cskilbeck/volume_knob/images/hid_configurator_1.png

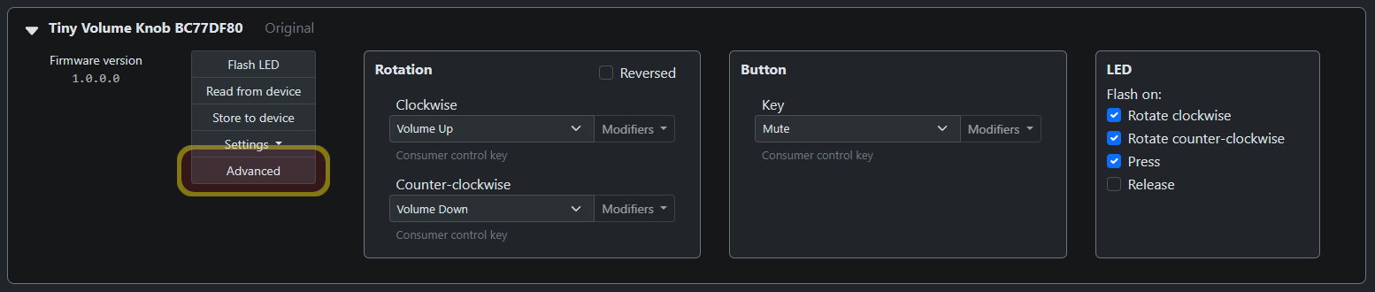
images/hid_configurator_1.png
