cskilbeck/volume_knob/pcb/wch554g/Outputs/2022-06-14/dfm.png

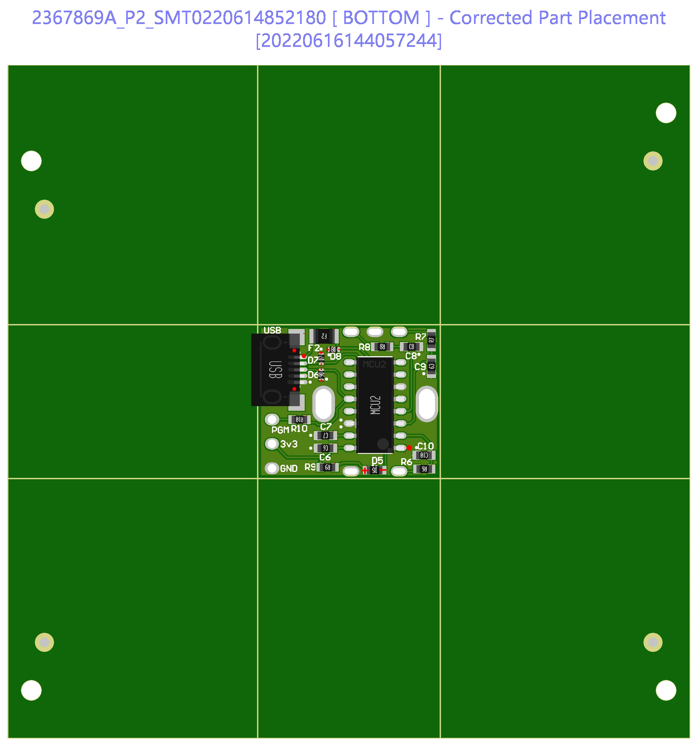
pcb/wch554g/Outputs/2022-06-14/dfm.png
