cskilbeck/volume_knob/enclosures/enclosure16x19/knob.SLDPRT

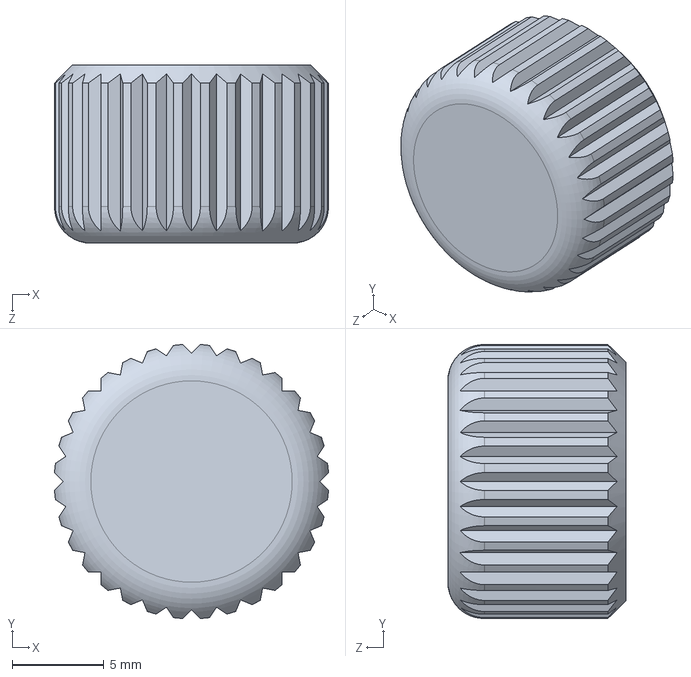
[picture p23: CAD file, 2022-03-15]
enclosures/enclosure16x19/knob.SLDPRT
15.0 x 15.0 x 9.75 mm
