cskilbeck/volume_knob/enclosures/enclosure_V2/enclosure_V2_lower.STEP

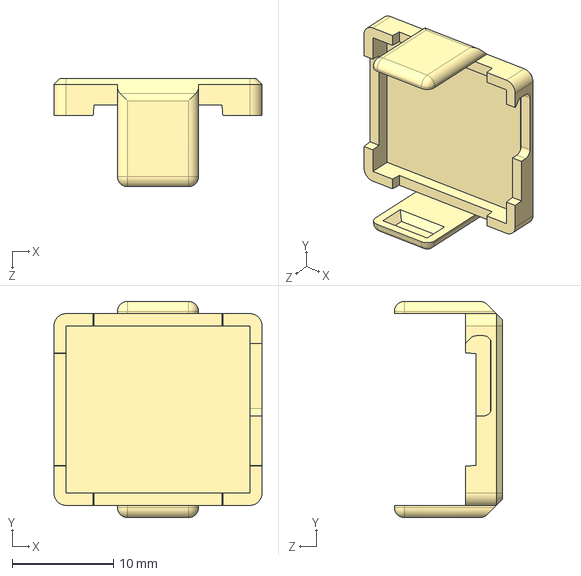
[picture p24: CAD file, 2025-02-15]
enclosures/enclosure_V2/enclosure_V2_lower.STEP
20.5 x 21.3 x 10.7 mm
