cskilbeck/volume_knob/enclosures/TUVK_Enclosure.step

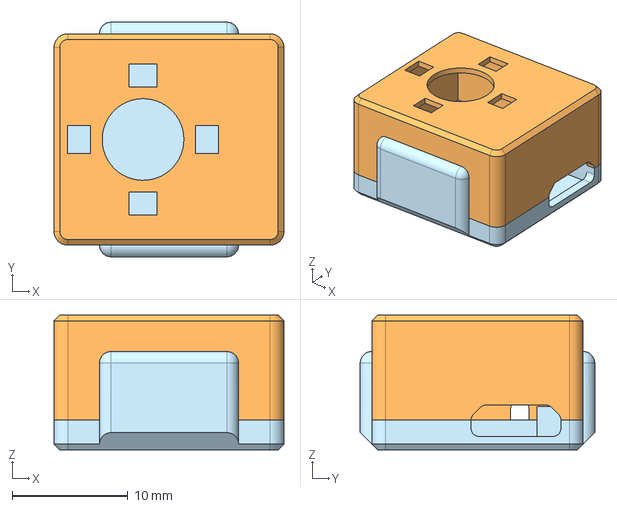
[picture p25: CAD file, 2026-02-22]
enclosures/TUVK_Enclosure.step
19.9 x 20.2 x 11.7 mm
