cskilbeck/volume_knob/pcb/wch554e/wch554e/Models/encoder.step

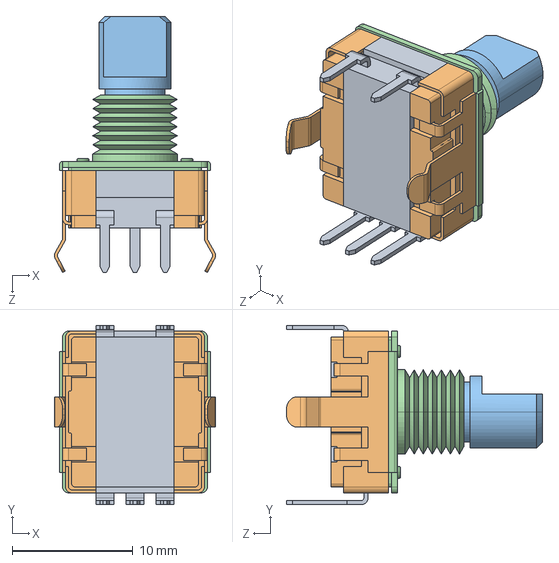
[picture p26: CAD file, 2022-03-15]
pcb/wch554e/wch554e/Models/encoder.step
13.4 x 14.9 x 21.2 mm
