cskilbeck/volume_knob/pcb/wch554g/models/U254-051T-4BH83-F1S--3DModel-STEP-510211.STEP

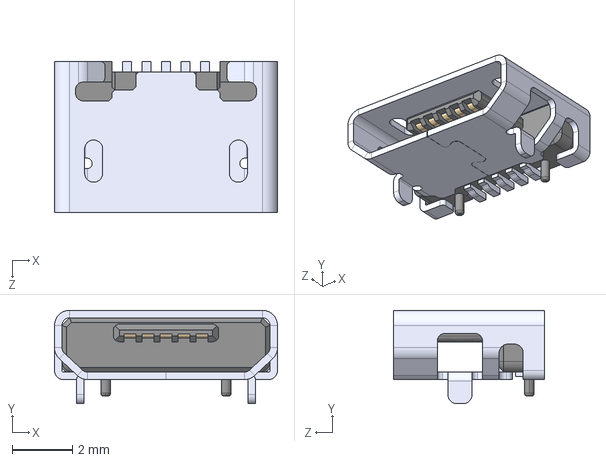
[picture p27: CAD file, 2023-11-22]
pcb/wch554g/models/U254-051T-4BH83-F1S--3DModel-STEP-510211.STEP
7.40 x 3.10 x 5.00 mm
