cskilbeck/volume_knob/enclosures/enclosure16x19/lower.SLDPRT

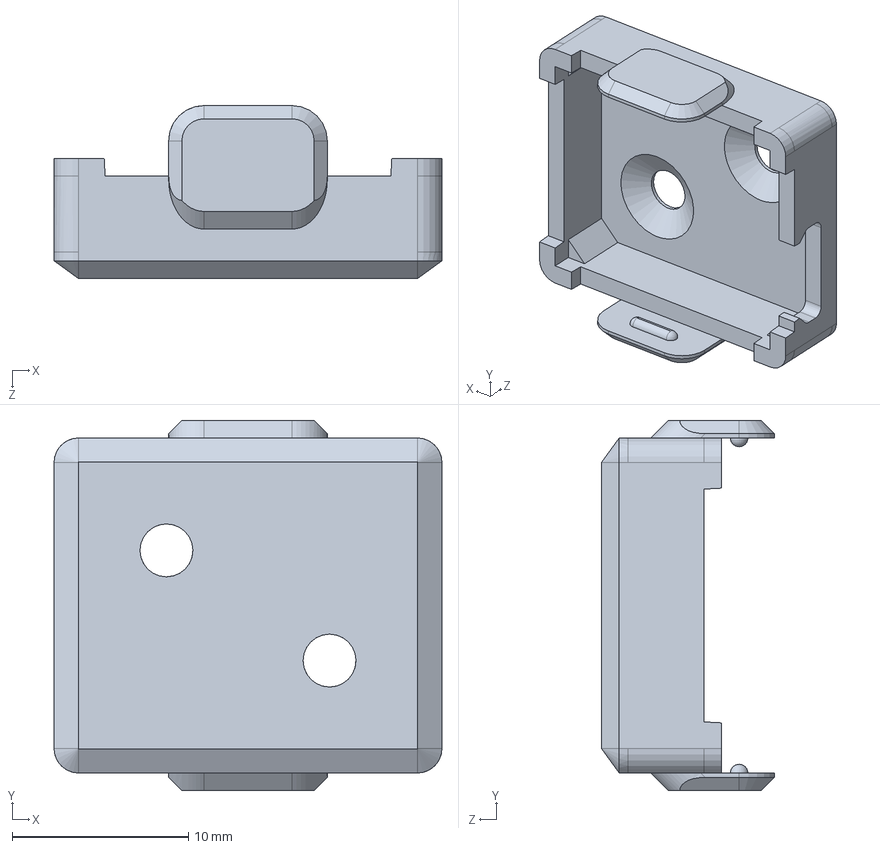
[picture p28: CAD file, 2022-03-15]
enclosures/enclosure16x19/lower.SLDPRT
22.0 x 21.0 x 9.80 mm
