cskilbeck/volume_knob/enclosures/enclosure_ch554e_80/knob.SLDPRT

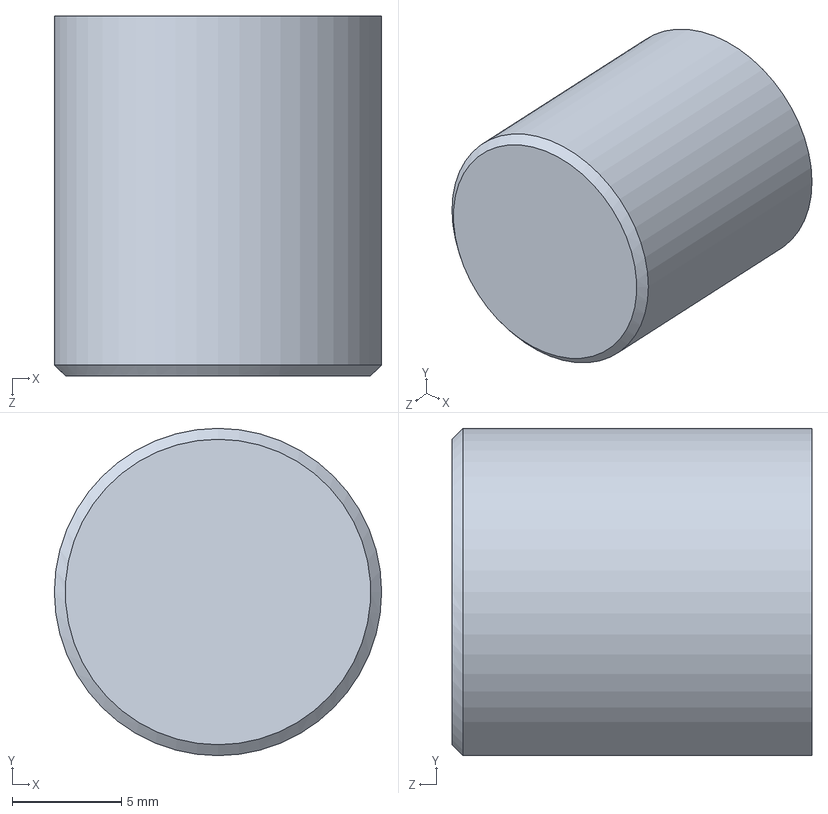
[picture p29: CAD file, 2024-07-27]
enclosures/enclosure_ch554e_80/knob.SLDPRT
15.0 x 15.0 x 16.5 mm
