cskilbeck/volume_knob/enclosures/enclosure_V2/enclosure_V2_upper.STEP

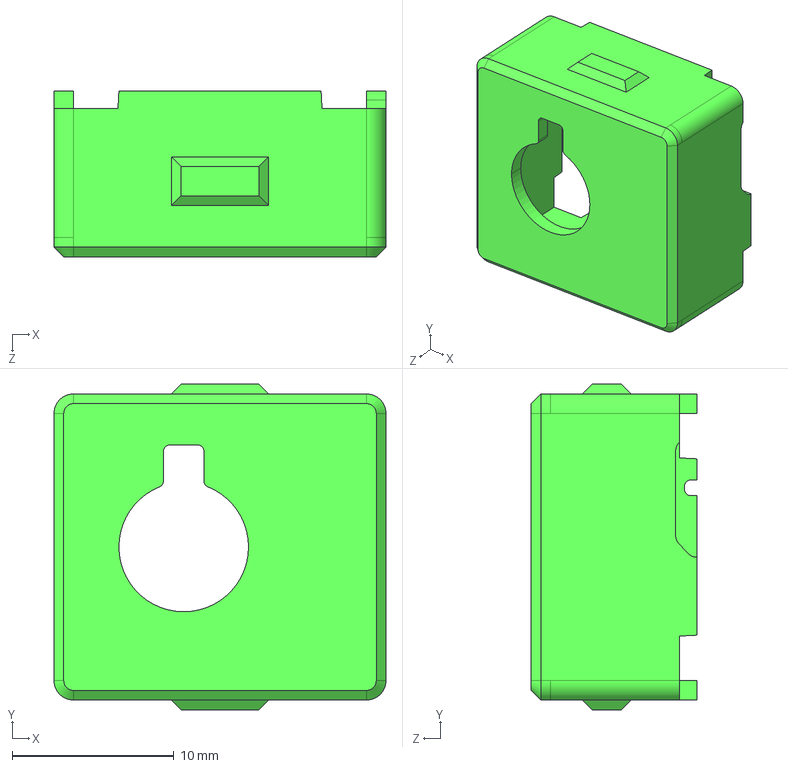
[picture p30: CAD file, 2025-02-15]
enclosures/enclosure_V2/enclosure_V2_upper.STEP
20.5 x 20.1 x 10.2 mm
