cskilbeck/volume_knob/enclosures/VK_D2.step

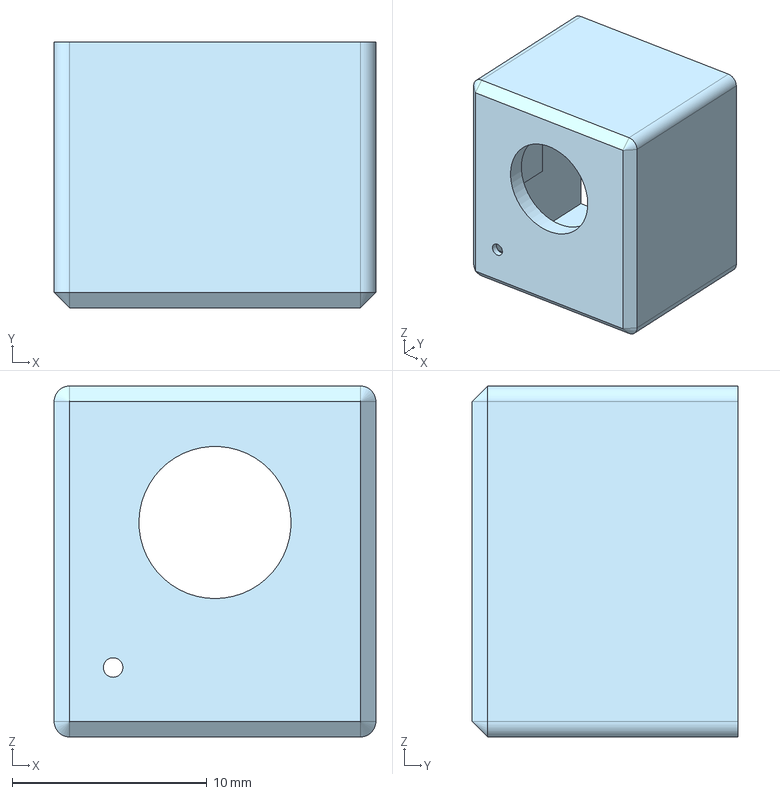
[picture p31: CAD file, 2026-02-22]
enclosures/VK_D2.step
16.5 x 13.7 x 18.0 mm
