cskilbeck/volume_knob/enclosures/enclosure_ch554e_80/lower.SLDPRT

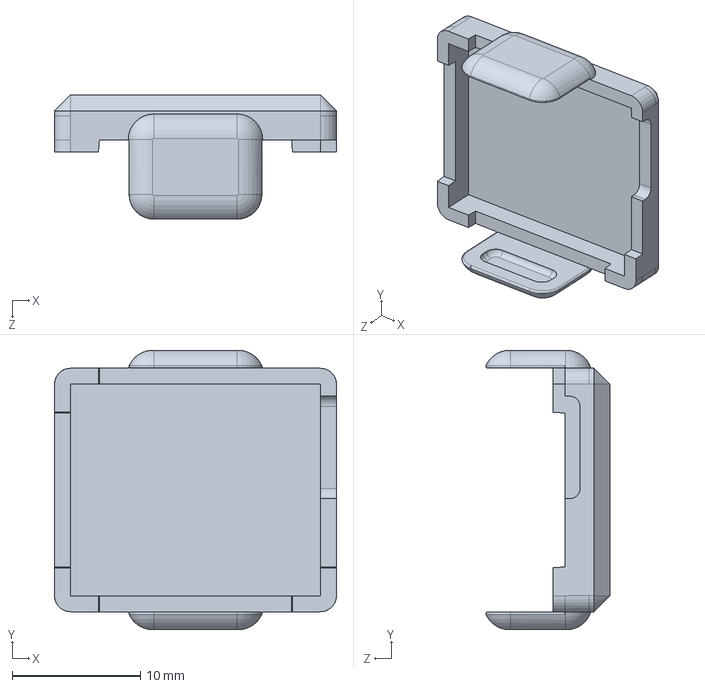
[picture p32: CAD file, 2024-06-04]
enclosures/enclosure_ch554e_80/lower.SLDPRT
22.0 x 21.8 x 9.71 mm
