cskilbeck/volume_knob/enclosures/enclosure16x19/encoder2.SLDPRT

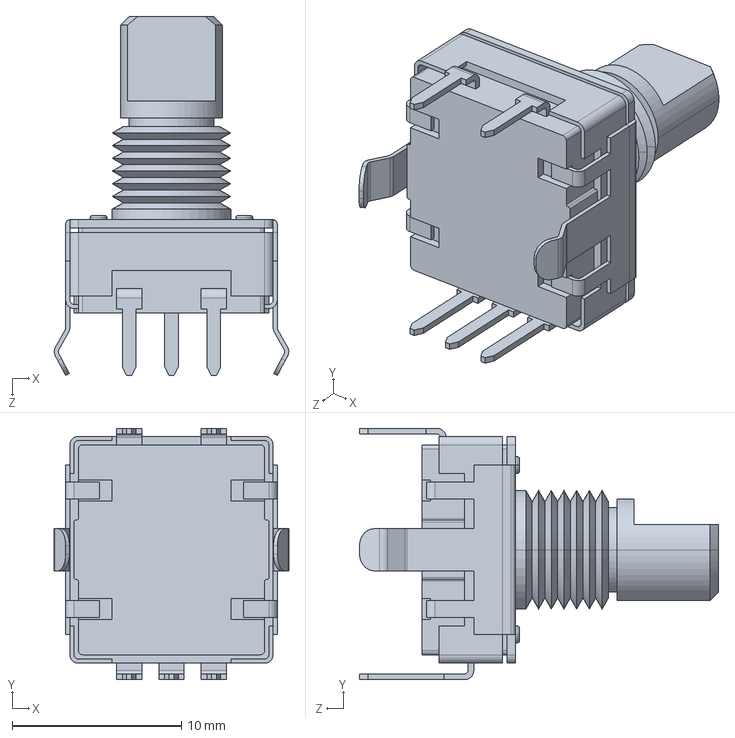
[picture p33: CAD file, 2022-03-15]
enclosures/enclosure16x19/encoder2.SLDPRT
13.9 x 14.9 x 21.2 mm
