cskilbeck/volume_knob/enclosures/enclosure_ch554e_80/upper.SLDPRT

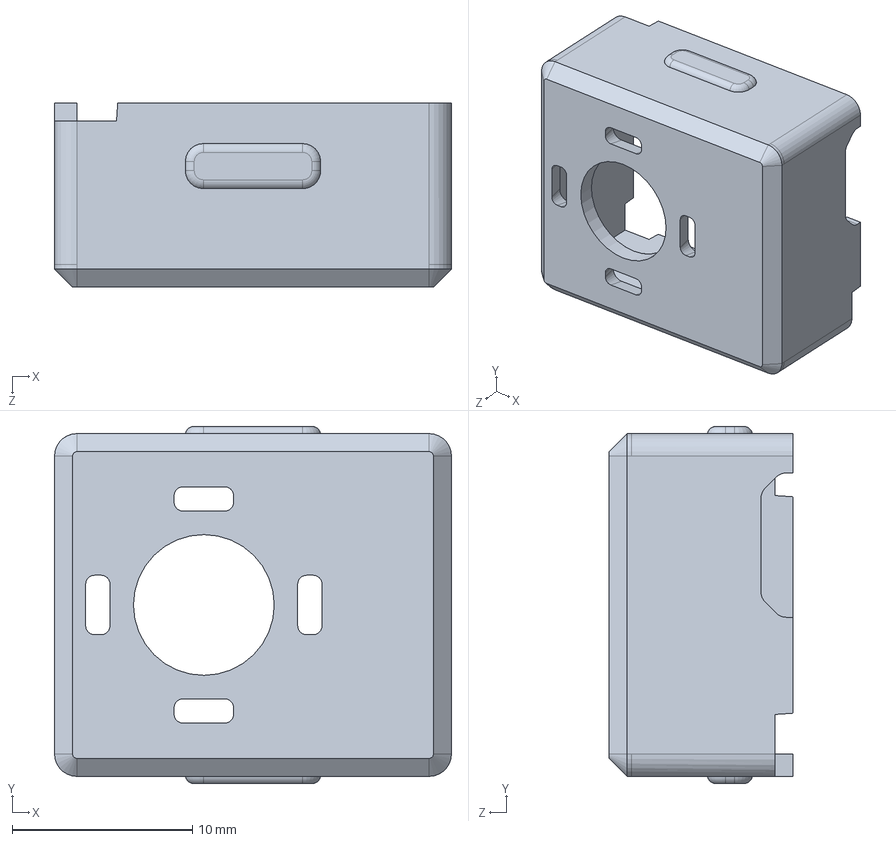
[picture p34: CAD file, 2024-06-04]
enclosures/enclosure_ch554e_80/upper.SLDPRT
22.0 x 19.8 x 10.2 mm
