cskilbeck/volume_knob/enclosures/enclosure_V2/PCB_V2.step

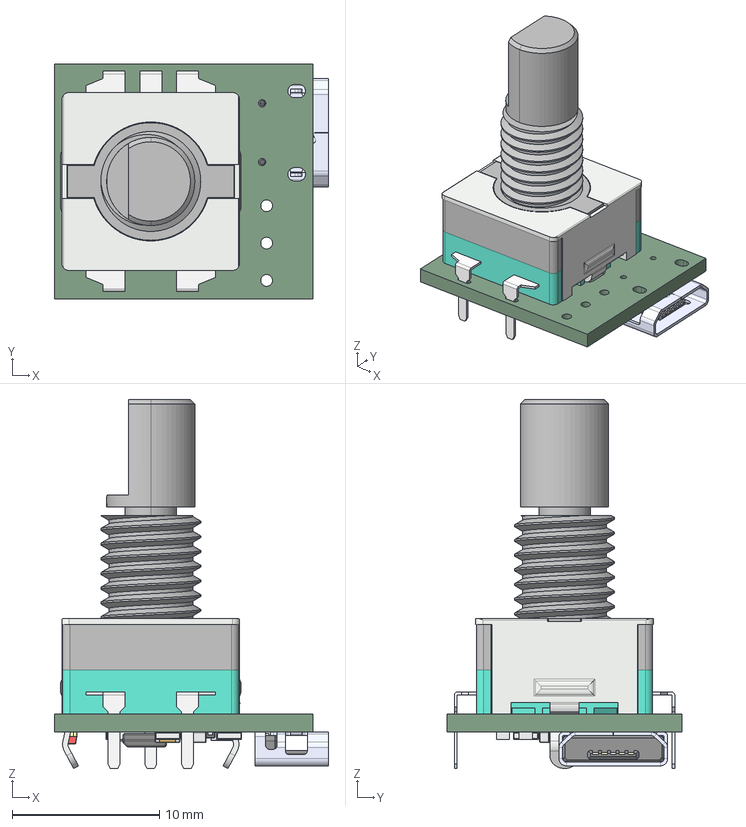
[picture p35: CAD file, 2024-10-21]
enclosures/enclosure_V2/PCB_V2.step
18.7 x 16.0 x 25.1 mm
Mid_Body x 5
Open_CASCADE_STEP_translator_6.8_12.2.1 x 11
Mark x 5
0603_Chip_SMD_LED_(1.6x0.8mm)_coloured
Open_CASCADE_STEP_translator_6.8_12.1
Leader x 10
rotary_encoder
U254-051T-4BH83-F1S_U254-051T-4BH83-F1S
FUSE_0603_1608_0.5MM
Open_CASCADE_STEP_translator_6.8_2.1.1 x 3
lead x 6
Open_CASCADE_STEP_translator_6.8_14.1.1 x 2
Open_CASCADE_STEP_translator_6.8_14.1.2 x 2
Open_CASCADE_STEP_translator_6.8_14.2.1 x 2
