cskilbeck/volume_knob/enclosures/enclosure_ch554e_80/usb_socket.STEP

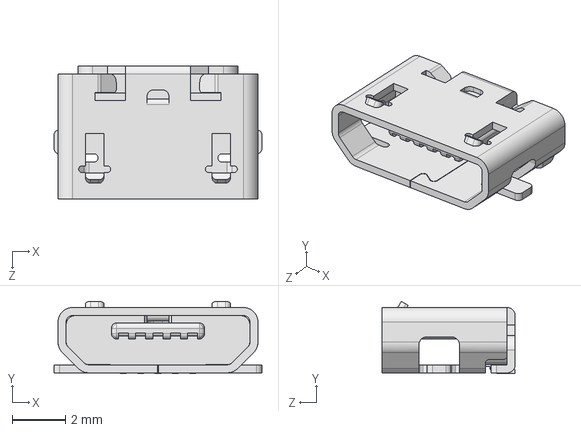
[picture p36: CAD file, 2024-03-06]
enclosures/enclosure_ch554e_80/usb_socket.STEP
7.80 x 2.71 x 5.00 mm
