cskilbeck/volume_knob/enclosures/enclosure_ch554e_80/board.SLDPRT

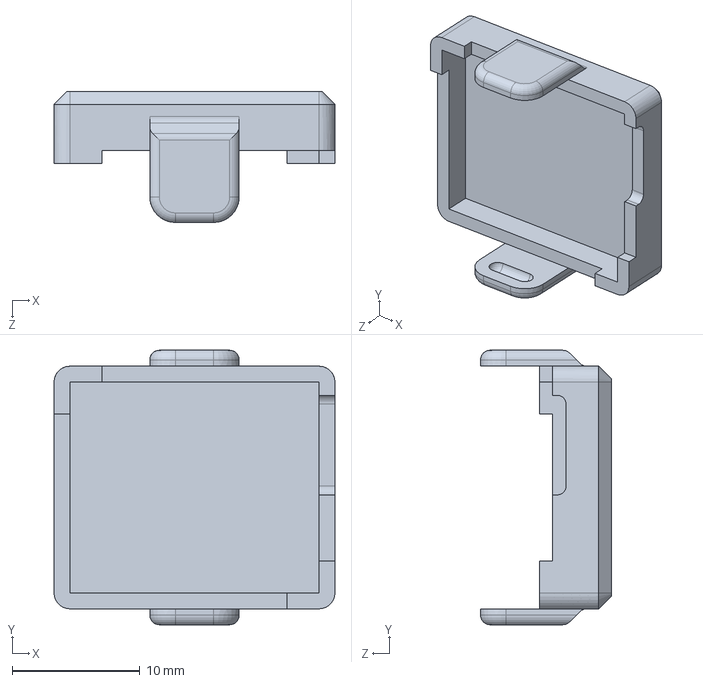
[picture p37: CAD file, 2022-04-18]
enclosures/enclosure_ch554e_80/board.SLDPRT
22.0 x 21.5 x 10.2 mm
