cskilbeck/volume_knob/pcb/wch554e/wch554e/Outputs/2022-03-28/wch554e.PDF

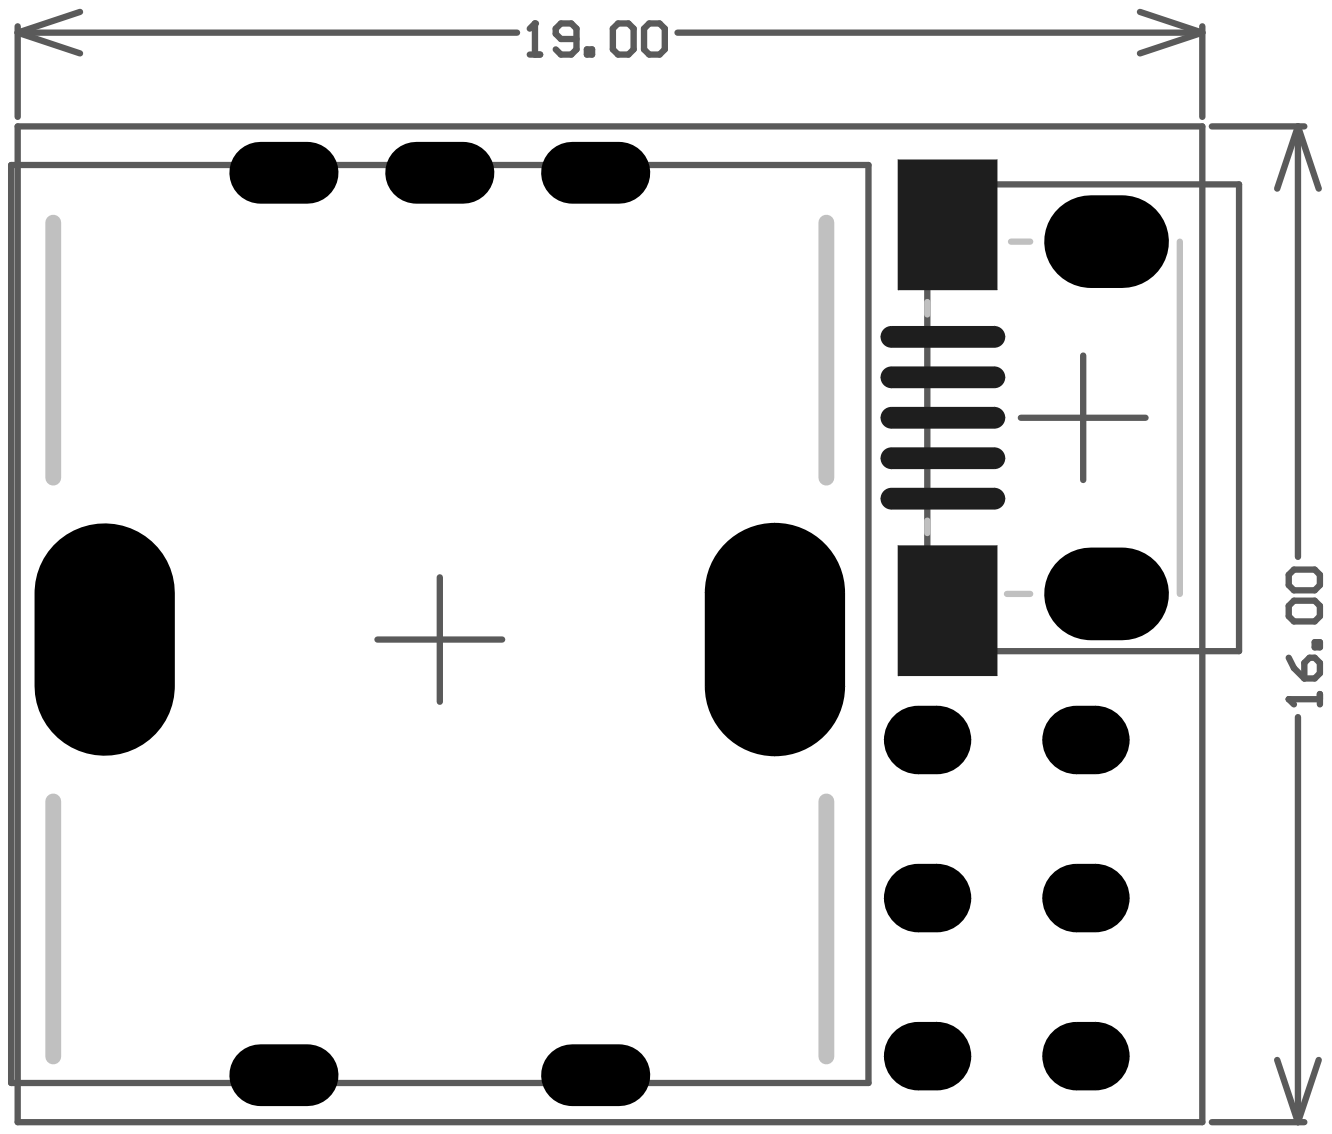
[picture p87: page 1]

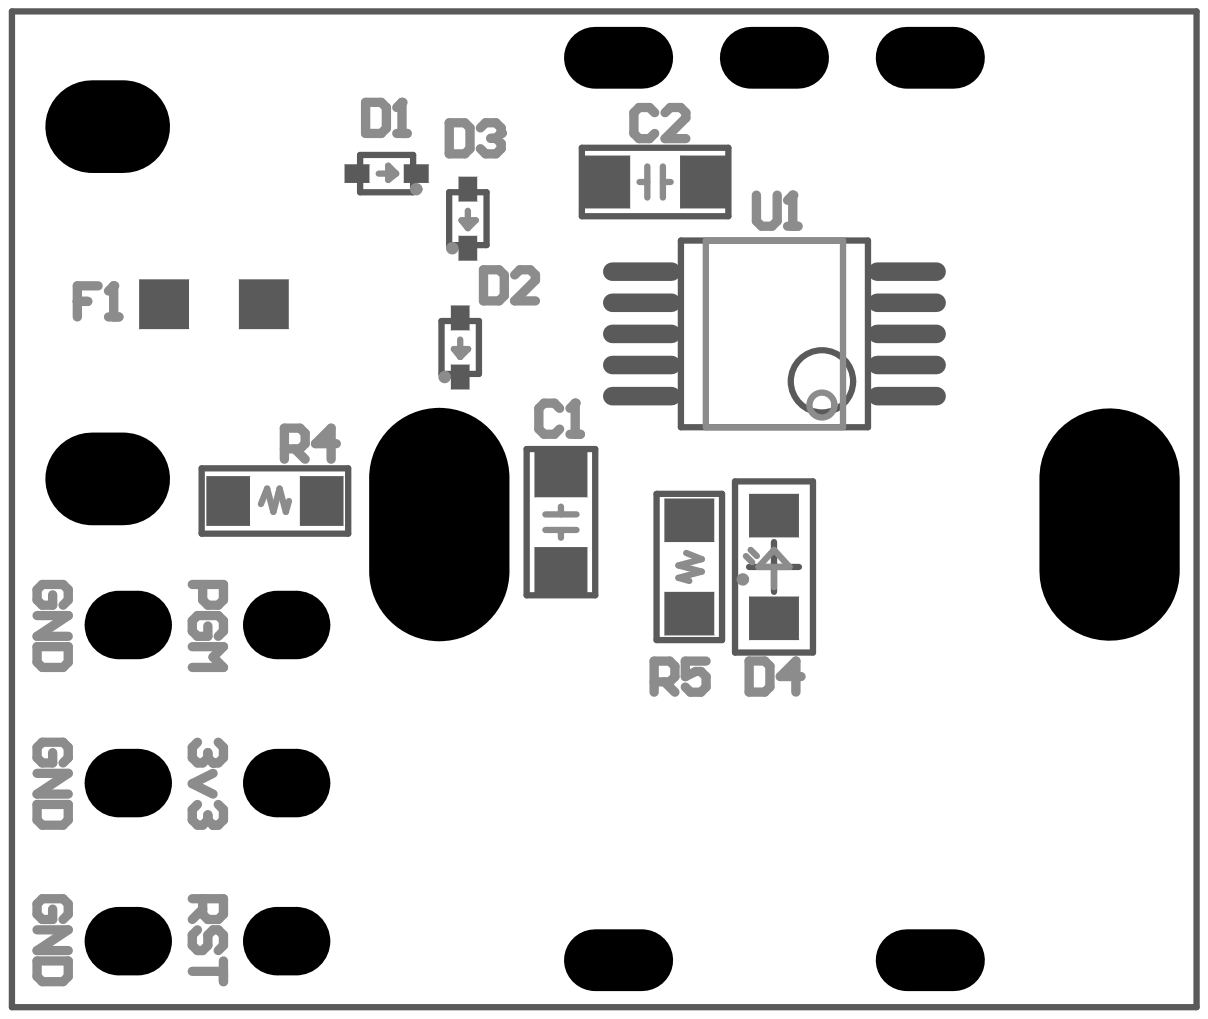
[picture p88: page 2]


P1.7/SCK/TXD1/TIN5 4

RST/T2EX_/CAP2_ 5 | DP | | D+ 3

Shield S

Designator | Quantity | Value | Description | Model:Footprint | Line #
U1 | 1 | | CH554E | MSOP10 3x3 x 0.5
DBG | 1 | | Debug header | 4 way debug header
F1 | 1 500mA | | FUSE | FUSE 0603
D4 | 1 20mA | | LED | SMT LED 0603
C1 | 1 1uF | | MLCC | MLCC 0603
C2 | 1 2.2uF | | MLCC | MLCC 0603
R4 | 1 10k | | Resistor | 0603 SMT Resistor
R5 | 1 1k | | Resistor | 0603 SMT Resistor
ROTARY_ENCODER | 1 | | Rotary Encoder | Rotary encoder
D1, D2, D3 | 3 | | TVS Diode | SODFL 98x40 2 pin
J1 | 1 | | USB Receptacle | USB Micro B Receptacle

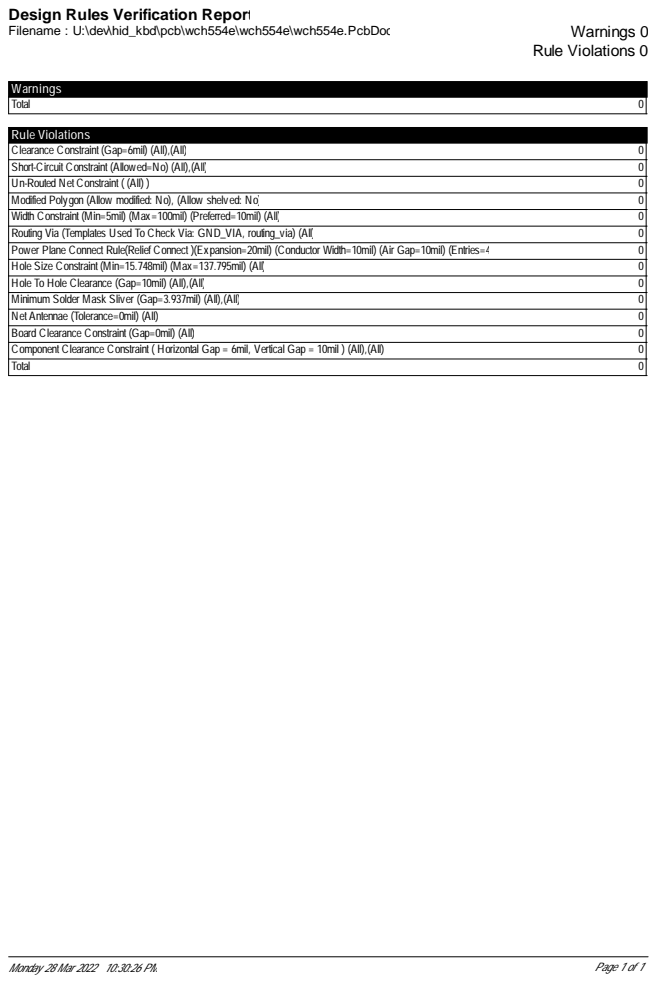
[picture p89: page 5]

Design Rules Verification Report
