cskilbeck/volume_knob/mic_muter/mic_muter/resource.h

//{{NO_DEPENDENCIES}}
// Microsoft Visual C++ generated include file.
// Used by mic_muter.rc
//
#define IDC_MYICON                      2
#define IDD_MICMUTER_DIALOG             102
#define IDS_APP_TITLE                   103
#define IDM_ABOUT                       104
#define IDI_MICMUTER                    107
#define IDC_MICMUTER                    109
#define ID_IMG_MUTED                    110
#define ID_IMG_NOT_MUTED                111
#define IDR_MAINFRAME                   128
#define IDI_ICON_MIC_GREEN              133
#define IDI_ICON_MIC_NORMAL             133
#define IDI_ICON_MIC_MUTE               134
#define IDR_MENU_POPUP                  135
#define IDI_ICON_MIC_MISSING            140
#define IDD_DIALOG_OPTIONS_OVERLAY      141
#define IDD_DIALOG_OPTIONS              142
#define IDC_SLIDER2                     1001
#define IDC_CHECK_RUN_AT_LOGIN          1003
#define IDC_CHECK_SHOW_WHEN_MUTED       1004
#define IDC_CHECK_SHOW_WHEN_UNMUTED     1005
#define IDC_SLIDER4                     1006
#define IDC_SLIDER5                     1007
#define IDC_SLIDER6                     1008
#define IDC_SLIDER7                     1009
#define IDC_STATIC_OVERLAY_POS          1012
#define IDC_CHECK_RUN_AT_STARTUP        1013
#define IDC_SLIDER1                     1022
#define IDC_COMBO_FADEOUT_AFTER         1023
#define IDC_COMBO_FADEOUT_TO            1024
#define IDC_COMBO_FADEOUT_SPEED         1025
#define IDC_CHECK_OVERLAY_ENABLE        1026
#define IDC_OPTIONS_TAB_CTRL            1037
#define IDC_STATIC_OPTIONS_OVERLAY_IMAGE 1038
#define IDC_BUTTON_CHOOSE_HOTKEY        1043
#define IDC_COMBO_HOTKEY                1046
#define IDC_CHECK_CTRL                  1047
#define IDC_CHECK_ALT                   1048
#define IDC_CHECK_SHIFT                 1049
#define IDC_CHECK4                      1050
#define IDC_CHECK_WINKEY                1050
#define IDC_STATIC_HOTKEY_MESSAGE       1051
#define ID_POPUP_QUIT                   32771
#define ID_POPUP_ETC                    32772
#define ID_POPUP_OPTIONS                32773
#define ID_POPUP_MUTE                   32774
#define ID_POPUP_MUTE2                  32775
#define ID_POPUP_OVERLAY                32776
#define ID_OVERLAY_POSITION             32777
#define ID_OVERLAY_MUTED                32778
#define ID_MUTED_ENABLE                 32779
#define ID_MUTED_FADEOUTAFTER           32780
#define ID_FADEOUTAFTER_1SECOND         32781
#define ID_FADEOUTAFTER_5SECONDS        32782
#define ID_FADEOUTAFTER_10SECONDS       32783
#define ID_FADEOUTAFTER_NEVER           32784
#define ID_MUTED_FADETO                 32785
#define ID_FADETO_INVISIBLE             32786
#define ID_OVERLAY_UNMUTED              32790
#define ID_UNMUTED_ENABLE               32791
#define ID_UNMUTED_FADEOUTAFTER         32792
#define ID_UNMUTED_FADETO               32797
#define ID_OPTIONS_RUNMICMUTERATLOGIN   32802
#define ID_POPUP_MICMUTER               32803
#define ID_POPUP_                       32804
#define ID_FADEOUTAFTER_1SECOND_MUTED   32805
#define ID_FADEOUTAFTER_5SECONDS_MUTED  32806
#define ID_FADEOUTAFTER_10SECONDS_MUTED 32807
#define ID_FADEOUTAFTER_NEVER_MUTED     32808
#define ID_FADETO_INVISIBLE_MUTED       32809
#define ID_FADETO_25_MUTED              32810
#define ID_FADETO_50_MUTED              32811
#define ID_FADEOUTAFTER_1SECOND_UNMUTED 32812
#define ID_FADEOUTAFTER_5SECONDS_UNMUTED 32813
#define ID_FADEOUTAFTER_10SECONDS_UNMUTED 32814
#define ID_FADEOUTAFTER_NEVER_UNMUTED   32815
#define ID_FADETO_INVISIBLE_UNMUTED     32816
#define ID_FADETO_25_UNMUTED            32817
#define ID_FADETO_50_UNMUTED            32818
#define ID_POPUP_ABOUTMICMUTER          32819
#define ID_MUTED_FADESPEED              32820
#define ID_FADESPEED_SLOW               32821
#define ID_FADESPEED_MEDIUM             32822
#define ID_FADESPEED_FAST               32823
#define ID_FADESPEED_IMMEDIATE          32824
#define ID_FADESPEED_SLOW_MUTED         32825
#define ID_FADESPEED_MEDIUM_MUTED       32826
#define ID_FADESPEED_FAST_MUTED         32827
#define ID_FADESPEED_IMMEDIATE_MUTED    32828
#define ID_FADESPEED_SLOW_UNMUTED       32829
#define ID_FADESPEED_MEDIUM_UNMUTED     32830
#define ID_FADESPEED_FAST_UNMUTED       32831
#define ID_FADESPEED_IMMEDIATE_UNMUTED  32832
#define ID_POPUP_SHOW_OPTIONS           32833
#define ID_POPUP_TOGGLE_MUTE            32834
#define ID_MOVE_OVERLAY                 32835
#define ID_POPUP_MOVE_OVERLAY           32836
#define IDC_STATIC                      -1

// Next default values for new objects
// 
#ifdef APSTUDIO_INVOKED
#ifndef APSTUDIO_READONLY_SYMBOLS
#define _APS_NO_MFC                     1
#define _APS_NEXT_RESOURCE_VALUE        143
#define _APS_NEXT_COMMAND_VALUE         32837
#define _APS_NEXT_CONTROL_VALUE         1052
#define _APS_NEXT_SYMED_VALUE           112
#endif
#endif
