cskilbeck/volume_knob/mic_muter/mic_muter/image.cpp

//////////////////////////////////////////////////////////////////////

#include "framework.h"

//////////////////////////////////////////////////////////////////////

namespace
{

#include "images/microphone_mute_svg.h"
#include "images/microphone_normal_svg.h"
#include "images/microphone_base_svg.h"

    char const *overlay_svg[chs::mic_muter::num_overlay_ids] = { microphone_mute_svg, microphone_normal_svg,
                                                                 microphone_base_svg };
}

namespace chs::mic_muter
{
    //////////////////////////////////////////////////////////////////////

    HRESULT image::create_solid(uint32 argb, int w, int h)
    {
        uint32 stride = w * sizeof(uint32);
        uint32 img_size = h * stride;

        BITMAPV5HEADER bmi{};
        bmi.bV5Size = sizeof(BITMAPV5HEADER);
        bmi.bV5Width = w;
        bmi.bV5Height = -h;
        bmi.bV5Planes = 1;
        bmi.bV5BitCount = 32;
        bmi.bV5Compression = BI_BITFIELDS;
        bmi.bV5SizeImage = img_size;
        bmi.bV5RedMask = 0x00ff0000;
        bmi.bV5GreenMask = 0x0000ff00;
        bmi.bV5BlueMask = 0x000000ff;
        bmi.bV5AlphaMask = 0xff000000;
        bmi.bV5CSType = LCS_WINDOWS_COLOR_SPACE;
        bmi.bV5Intent = LCS_GM_GRAPHICS;

        BITMAPINFO src_bmi{};
        src_bmi.bmiHeader.biSize = sizeof(BITMAPINFOHEADER);
        src_bmi.bmiHeader.biWidth = w;
        src_bmi.bmiHeader.biHeight = -h;
        src_bmi.bmiHeader.biPlanes = 1;
        src_bmi.bmiHeader.biBitCount = 32;
        src_bmi.bmiHeader.biCompression = BI_RGB;

        dc = CreateCompatibleDC(nullptr);

        uint32 *buffer = new uint32[img_size];

        for(uint32 i = 0; i < img_size; ++i) {
            buffer[i] = argb;
        }

        DEFER(delete[] buffer);

        bmp = CreateDIBitmap(dc, (BITMAPINFOHEADER const *)&bmi, CBM_INIT, buffer, &src_bmi, DIB_RGB_COLORS);
        if(bmp == nullptr) {
            return WIN32_LAST_ERROR("CreateDIBitmap");
        }
        width = w;
        height = h;
        old_bmp = SelectObject(dc, bmp);
        return S_OK;
    }

    //////////////////////////////////////////////////////////////////////

    HRESULT image::create_from_svg(char const *svg, int w, int h)
    {
        destroy();

        HR(util::svg_to_bitmap(svg, w, h, &bmp));
        width = w;
        height = h;
        dc = CreateCompatibleDC(nullptr);
        old_bmp = SelectObject(dc, bmp);
        return S_OK;
    }

    //////////////////////////////////////////////////////////////////////

    void image::destroy()
    {
        if(old_bmp != nullptr && dc != nullptr) {
            SelectObject(dc, old_bmp);
            old_bmp = nullptr;
        }
        if(bmp != nullptr) {
            DeleteObject(bmp);
            bmp = nullptr;
        }
        if(dc != nullptr) {
            DeleteDC(dc);
            dc = nullptr;
        }
    }

    //////////////////////////////////////////////////////////////////////

    char const *get_overlay_svg(overlay_id id)
    {
        int index = std::clamp(static_cast<int>(id), 0, max_overlay_id);
        return overlay_svg[index];
    }
}
