cskilbeck/volume_knob/ch554_firmware/common/include/types.h

#pragma once

//////////////////////////////////////////////////////////////////////

#include <stdint.h>

typedef int8_t int8;
typedef int16_t int16;
typedef int32_t int32;

typedef uint8_t uint8;
typedef uint16_t uint16;
typedef uint32_t uint32;
