cskilbeck/volume_knob/ch554_firmware/common/include/xdata_common.h

// DO NOT PUT #pragma once in here!

//////////////////////////////////////////////////////////////////////

#if !defined(XDATA)
#define XDATA extern __xdata
#endif

#include "types.h"

XDATA uint8 usb_endpoint_0_buffer[USB_PACKET_SIZE];

XDATA uint8 usb_endpoint_1_rx_buffer[USB_PACKET_SIZE];
XDATA uint8 usb_endpoint_1_tx_buffer[USB_PACKET_SIZE];
XDATA uint8 usb_endpoint_2_rx_buffer[USB_PACKET_SIZE];
XDATA uint8 usb_endpoint_2_tx_buffer[USB_PACKET_SIZE];
XDATA uint8 usb_endpoint_3_rx_buffer[USB_PACKET_SIZE];
XDATA uint8 usb_endpoint_3_tx_buffer[USB_PACKET_SIZE];

#define SERIAL_LEN 8    // 8 chars for 32 bit hex serial # from chip_id 01234567

// serial number stuff - see usb_init_strings()
XDATA uint8 serial_number_string[(2 + 2 * SERIAL_LEN)];    // e.g "012345678"
XDATA uint8 product_name_string[(2 + 2 * 48)];             // Max product name is 24 + 8

XDATA struct usb_data usb;

XDATA struct save_buffer save_buffer;

#undef XDATA
