cskilbeck/volume_knob/ch554_firmware/common/include/tick.h

#pragma once

//////////////////////////////////////////////////////////////////////
// TIMER0 = LED pwm
// TIMER1 = UART
// TIMER2 = 1KHz tick

//////////////////////////////////////////////////////////////////////

extern uint16 ticks;

void tick_init();
void tick_wait(uint16 n);
