cskilbeck/volume_knob/mic_muter/common_lib/framework.h

//////////////////////////////////////////////////////////////////////

#pragma once

//////////////////////////////////////////////////////////////////////

#define NOMINMAX
#define WIN32_LEAN_AND_MEAN

#define _WIN32_WINNT _WIN32_WINNT_WIN7

#include <windows.h>
#include <wrl/client.h>
#include <wincodec.h>

//////////////////////////////////////////////////////////////////////

#include <vector>
#include <mutex>
#include <format>

//////////////////////////////////////////////////////////////////////

#include "ansi.h"
#include "logger.h"
#include "../lunasvg-2.3.4/include/lunasvg.h"
#include "util.h"
