cskilbeck/volume_knob/mic_muter/mic_muter/pch.cpp

#include "framework.h"

#pragma comment(lib, "uxtheme.lib")
#pragma comment(lib, "comctl32.lib")
#pragma comment(lib, "Msimg32.lib")

#pragma comment(linker,                                                                                         \
                "/manifestdependency:\"type='win32' name='Microsoft.Windows.Common-Controls' version='6.0.0.0'" \
                " processorArchitecture='*' publicKeyToken='6595b64144ccf1df' language='*'\"")
